Yercar18/Dronefenix/AirQ_Wemos/PROCESS_DATA.cpp

#include "PROCESS_DATA.h"
#include <ArduinoJson.h>
#include "configuration.h"

int PROCESS_DATA::getIndex()
{
  return msqQeueCounter;
}
void PROCESS_DATA::setTimeToWait(int time)
{
  timeWait = time;
if(serDebug) Serial.println("Tiempo de espera para publicar(minutos): " + String(time));
}

int PROCESS_DATA::generateRandom()
{
  return random(1,20);
}

void PROCESS_DATA::resetMsgQeueCounter()
{
  msqQeueCounter = 1;
}

String PROCESS_DATA::getJSON(int index)
{
  return msqQeue[index];
}

boolean PROCESS_DATA::SAVEJSON(String JSON)
{
    if (serDebug & msqQeueCounter<60) Serial.println("Mensaje guardado - " + String(msqQeueCounter));
    if (serDebug & msqQeueCounter==60) Serial.println("publicando sesenta topics");
    
    unsigned long tiempominutos = (millis()-oldTimeSended)/(60*1000);
    Serial.println("Tiempo minutos: " + String(tiempominutos));
    Serial.println("Time to wait: " + String(timeWait));

    if(msqQeueCounter < 60 &  tiempominutos<timeWait)
    {
      msqQeue[msqQeueCounter] = JSON; 
      msqQeueCounter++;
      return false;
    }
    else
    { 
      oldTimeSended =  millis();
      if (serDebug & msqQeueCounter!=60) Serial.println("publicando " + String(msqQeueCounter) + " topics");     
      return true;
    }
}


String PROCESS_DATA::ensamblarMensajeJSON(int temp, int hum, int presAlt, int alcoholPPM, int TVOC, int CO2, int CH4, int NH4, float latitud, float longitud, String fecha){
     // Memory pool for JSON object tree.
    //
    // Inside the brackets, 200 is the size of the pool in bytes.
    // Don't forget to change this value to match your JSON document.
    // Use arduinojson.org/assistant to compute the capacity.
    DynamicJsonBuffer jsonBuffer(260);
    // StaticJsonBuffer allocates memory on the stack, it can be
    // replaced by DynamicJsonBuffer which allocates in the heap.
    //
    // DynamicJsonBuffer  jsonBuffer(200);
    
    // Create the root of the object tree.
    //
    // It's a reference to the JsonObject, the actual bytes are inside the
    // JsonBuffer with all the other nodes of the object tree.
    // Memory is freed when jsonBuffer goes out of scope.
    JsonObject& root = jsonBuffer.createObject();         
    root["D1"] = temp;  
    root["D2"] = hum; 
    root["D3"] = presAlt;  
    root["D4"] = alcoholPPM>1000?1000:NH4;  //From MQ4 Datasheet
    root["D5"] = TVOC;  
    root["D6"] = CO2; 
    root["D7"] = CH4;  
    root["D8"] = NH4>1000?1000:NH4;  //From MQ4 Datasheet
        
    root["D9"] =  latitud>0?String(latitud,5):"0"; 
    root["D10"] = longitud>0?String(longitud,5):"0"; 
    root["D11"] = fecha;
        
    char JSONmessageBuffer[260];
    root.printTo(JSONmessageBuffer, sizeof(JSONmessageBuffer));
    return JSONmessageBuffer;
}


double PROCESS_DATA::leerTemperatura()
{
  return stringToDouble(temp);
}
double PROCESS_DATA::leerHumedad()
{
  return stringToDouble(hum);
}
double PROCESS_DATA::leerPresionAtmosferica()
{
  return stringToDouble(presAt);
}
int PROCESS_DATA::leerTVOC()
{
  return stringToDouble(tvoc);
}
int PROCESS_DATA::leerAlcohol()
{
  return stringToDouble(alcohol);
}
int PROCESS_DATA::leerCO2()
{
  return stringToDouble(co2);
}
int PROCESS_DATA::leerCH4()
{
  return stringToDouble(CH4);
}
int PROCESS_DATA::leerNH4()
{
  return stringToDouble(NH4);
}
float PROCESS_DATA::leerLatitud()
{
  return stringToDouble(latitud);
}
float PROCESS_DATA::leerLongitud()
{
  return stringToDouble(longitud);
}
double PROCESS_DATA::leerFecha()
{
  return stringToDouble(fecha);
}

String PROCESS_DATA::mensajeSDTabulado()
{
  return temp + tabulador + hum + tabulador + presAt + tabulador + alcohol + tabulador +tvoc + tabulador + co2 + tabulador + CH4 + tabulador + NH4 + tabulador + latitud + tabulador + longitud + tabulador + fecha;
}
void PROCESS_DATA::setFecha(String fechaIn)
{
  fecha = fechaIn;
}
bool PROCESS_DATA::procesarInformacion(String Data)
{
    //Elimniar espacios en blanco
    Data.trim();

    if(Data.length() >10)
    {
      int valuePointer = 0;
      String initCharacterReceived = "";
      while(initCharacterReceived!=initialCharacter && valuePointer<=5){
        initCharacterReceived = getValueStr(Data,tabulador,valuePointer);
        valuePointer++;
      }
      temp = getValueStr(Data,tabulador,valuePointer).toInt() > 0 ? getValueStr(Data,tabulador,valuePointer):"0";
      valuePointer++;
      hum = getValueStr(Data,tabulador,valuePointer).toInt() > 0 ? getValueStr(Data,tabulador,valuePointer):"0";
      valuePointer++;
      presAt = getValueStr(Data,tabulador,valuePointer).toInt() > 0 ? getValueStr(Data,tabulador,valuePointer):"0";
      valuePointer++;
      alcohol = getValueStr(Data,tabulador,valuePointer).toInt() > 0 ? getValueStr(Data,tabulador,valuePointer):"0";
      valuePointer++;
      tvoc = getValueStr(Data,tabulador,valuePointer).toInt() > 0 ? getValueStr(Data,tabulador,valuePointer):"0";
      valuePointer++;
      co2 = getValueStr(Data,tabulador,valuePointer).toInt() > 0 ? getValueStr(Data,tabulador,valuePointer):"0";
      valuePointer++;
      CH4 = getValueStr(Data,tabulador,valuePointer).toInt() > 0 ? getValueStr(Data,tabulador,valuePointer):"0";
      valuePointer++;
      NH4 = abs(getValueStr(Data,tabulador,valuePointer).toInt()) > 0 ? getValueStr(Data,tabulador,valuePointer):"0";
      valuePointer++;
  
      latitud = abs(getValueStr(Data,tabulador,valuePointer).toInt()) > 0 ? getValueStr(Data,tabulador,valuePointer):"0";
      valuePointer++;
      longitud = abs(getValueStr(Data,tabulador,valuePointer).toInt()) > 0 ? getValueStr(Data,tabulador,valuePointer):"0";
      valuePointer++;
      //fecha = abs(getValueStr(Data,tabulador,valuePointer).toInt()) > 0 ? getValueStr(Data,tabulador,valuePointer):"0";
      valuePointer++;
      
      String endCharacterReceived = getValueStr(Data,tabulador,valuePointer);
      
      if(strcmp(initCharacterReceived.c_str(), initialCharacter)>=0 && strcmp(endCharacterReceived.c_str(), endCharacter)>=0)
      {
        if(serDebug) Serial.println("La informacion leida es valida");
        return true;
      }
      else
      {
        if(serDebug) Serial.print("Data invalida - ");
        if(serDebug) Serial.println("Caracter de inicio: " + initCharacterReceived + " caracter de fin: " + endCharacterReceived);
        if(serDebug) Serial.println("Comparacion de string de  inicio: " + String(strcmp(initCharacterReceived.c_str(), initialCharacter)));
        if(serDebug) Serial.println("Comparacion de string de  Final: " + String(strcmp(endCharacterReceived.c_str(), endCharacter)));
        return false;
      }
    }
    else
    {
      //Si no ha leido data
      return false;
    }
}

bool PROCESS_DATA::getValue(String data, char tabuladorarator, int index)
{
    int found = 0;
    int strIndex[] = { 0, -1 };
    int maxIndex = data.length();

    for (int i = 0; i <= maxIndex && found <= index; i++) {
        if (data.charAt(i) == tabuladorarator || i == maxIndex) {
            found++;
            strIndex[0] = strIndex[1] + 1;
            strIndex[1] = (i == maxIndex) ? i+1 : i;
        }
    }
    return found > index ? data.substring(strIndex[0], strIndex[1]).toInt()>=0 : false;
}

String PROCESS_DATA::getValueStr(String data, char tabuladorarator, int index)
{
    int found = 0;
    int strIndex[] = { 0, -1 };
    int maxIndex = data.length();

    for (int i = 0; i <= maxIndex && found <= index; i++) {
        if (data.charAt(i) == tabuladorarator || i == maxIndex) {
            found++;
            strIndex[0] = strIndex[1] + 1;
            strIndex[1] = (i == maxIndex) ? i+1 : i;
        }
    }
    return found > index ? data.substring(strIndex[0], strIndex[1]) : "0";
}

double PROCESS_DATA::stringToDouble(String & str)  // <-- notice the "&"
{
  return atof( str.c_str() );
}
