Yercar18/Dronefenix/airQ_Arduino/SERIAL_COMMUNICATION.cpp

#include "SERIAL_COMMUNICATION.h"
#include "configuration.h"
#include <SoftwareSerial.h>

SoftwareSerial weMoSerial(wRx,wTx);


void SERIAL_COMMUNICATION::inicializar(){
  if(serDebug) Serial.begin(baudRateDebug);
  weMoSerial.begin(baudRateDebug);
}

void SERIAL_COMMUNICATION::enviarWemos(String mensaje){
  weMoSerial.println(mensaje);
}
