Yercar18/Dronefenix/airQ_Arduino/SERIAL_COMMUNICATION.h

#ifndef SERIAL_COMMUNICATION_H
#define SERIAL_COMMUNICATION_H

#include "Arduino.h"

class SERIAL_COMMUNICATION {
  public:
    void inicializar();
    void enviarWemos(String mensaje);
};


#endif // SERIAL_COMMUNICATION_H
